nygma2004/Wifi_Throttle/icons.h

// 'blank', 16x16px
const uint8_t icon_blank[32] PROGMEM = {
0xff, 0xff, 
0xff, 0xff, 
0xff, 0xff, 
0xff, 0xff, 
0xff, 0xff, 
0xff, 0xff, 
0xff, 0xff, 
0xff, 0xff, 
0xff, 0xff, 
0xff, 0xff, 
0xff, 0xff, 
0xff, 0xff, 
0xff, 0xff, 
0xff, 0xff, 
0xff, 0xff, 
0xff, 0xff
};

// 'left direction arrow', 15x80px
const uint8_t dir_left[1200] PROGMEM = {
0x00, 0x02, 
0x00, 0x04, 
0x00, 0x06, 
0x00, 0x04, 
0x00, 0x0e, 
0x00, 0x0c, 
0x00, 0x0a, 
0x00, 0x1c, 
0x00, 0x1e, 
0x00, 0x14, 
0x00, 0x3e, 
0x00, 0x3c, 
0x00, 0x3a, 
0x00, 0x7c, 
0x00, 0x7e, 
0x00, 0xf4, 
0x00, 0xfe, 
0x00, 0xfc, 
0x01, 0xfa, 
0x01, 0xfc, 
0x01, 0xf6, 
0x03, 0xfc, 
0x03, 0xfa, 
0x03, 0xfc, 
0x07, 0xf6, 
0x07, 0xfc, 
0x0f, 0xfa, 
0x0f, 0xfc, 
0x0f, 0xf6, 
0x1f, 0xfc, 
0x1f, 0xfa, 
0x1f, 0xfc, 
0x3f, 0xfa, 
0x3f, 0xf4, 
0x3f, 0xfa, 
0x7f, 0xf4, 
0x7f, 0xea, 
0x7f, 0xf4, 
0xff, 0xfa, 
0xff, 0xd4, 
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
};

// 'right direction arrow', 15x80px
const uint8_t dir_right[1200] PROGMEM = {
0x80, 0x00, 
0x40, 0x00, 
0xc0, 0x00, 
0x40, 0x00, 
0xe0, 0x00, 
0x60, 0x00, 
0xa0, 0x00, 
0x70, 0x00, 
0xf0, 0x00, 
0x50, 0x00, 
0xf8, 0x00, 
0x78, 0x00, 
0xb8, 0x00, 
0x7c, 0x00, 
0xfc, 0x00, 
0x5e, 0x00, 
0xfe, 0x00, 
0x7e, 0x00, 
0xbf, 0x00, 
0x7f, 0x00, 
0xdf, 0x00, 
0x7f, 0x80, 
0xbf, 0x80, 
0x7f, 0x80, 
0xdf, 0xc0, 
0x7f, 0xc0, 
0xbf, 0xe0, 
0x7f, 0xe0, 
0xdf, 0xe0, 
0x7f, 0xf0, 
0xbf, 0xf0, 
0x7f, 0xf0, 
0xbf, 0xf8, 
0x5f, 0xf8, 
0xbf, 0xf8, 
0x5f, 0xfc, 
0xaf, 0xfc, 
0x5f, 0xfc, 
0xbf, 0xfe, 
0x57, 0xfe, 
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
};

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
};
